nakujaproject/LIquid-Rocket-Engine-Development/code/test/include/config.h

// Variables for connecting to the WiFi network
const char* ssid = "yourSSID";
const char* password = "yourPassword";

// Variables for connecting to the MQTT broker
const char* mqttServer = "yourMQTTServerIPAddress";
const int mqttPort = 1883;
const char* mqttUsername = "yourMQTTUsername";
const char* mqttPassword = "yourMQTTPassword";
